xaratustrah/rdts/rsrc/rdts.kicad_sch

## KiCad design rsrc/rdts.kicad_sch (2023-10-17)

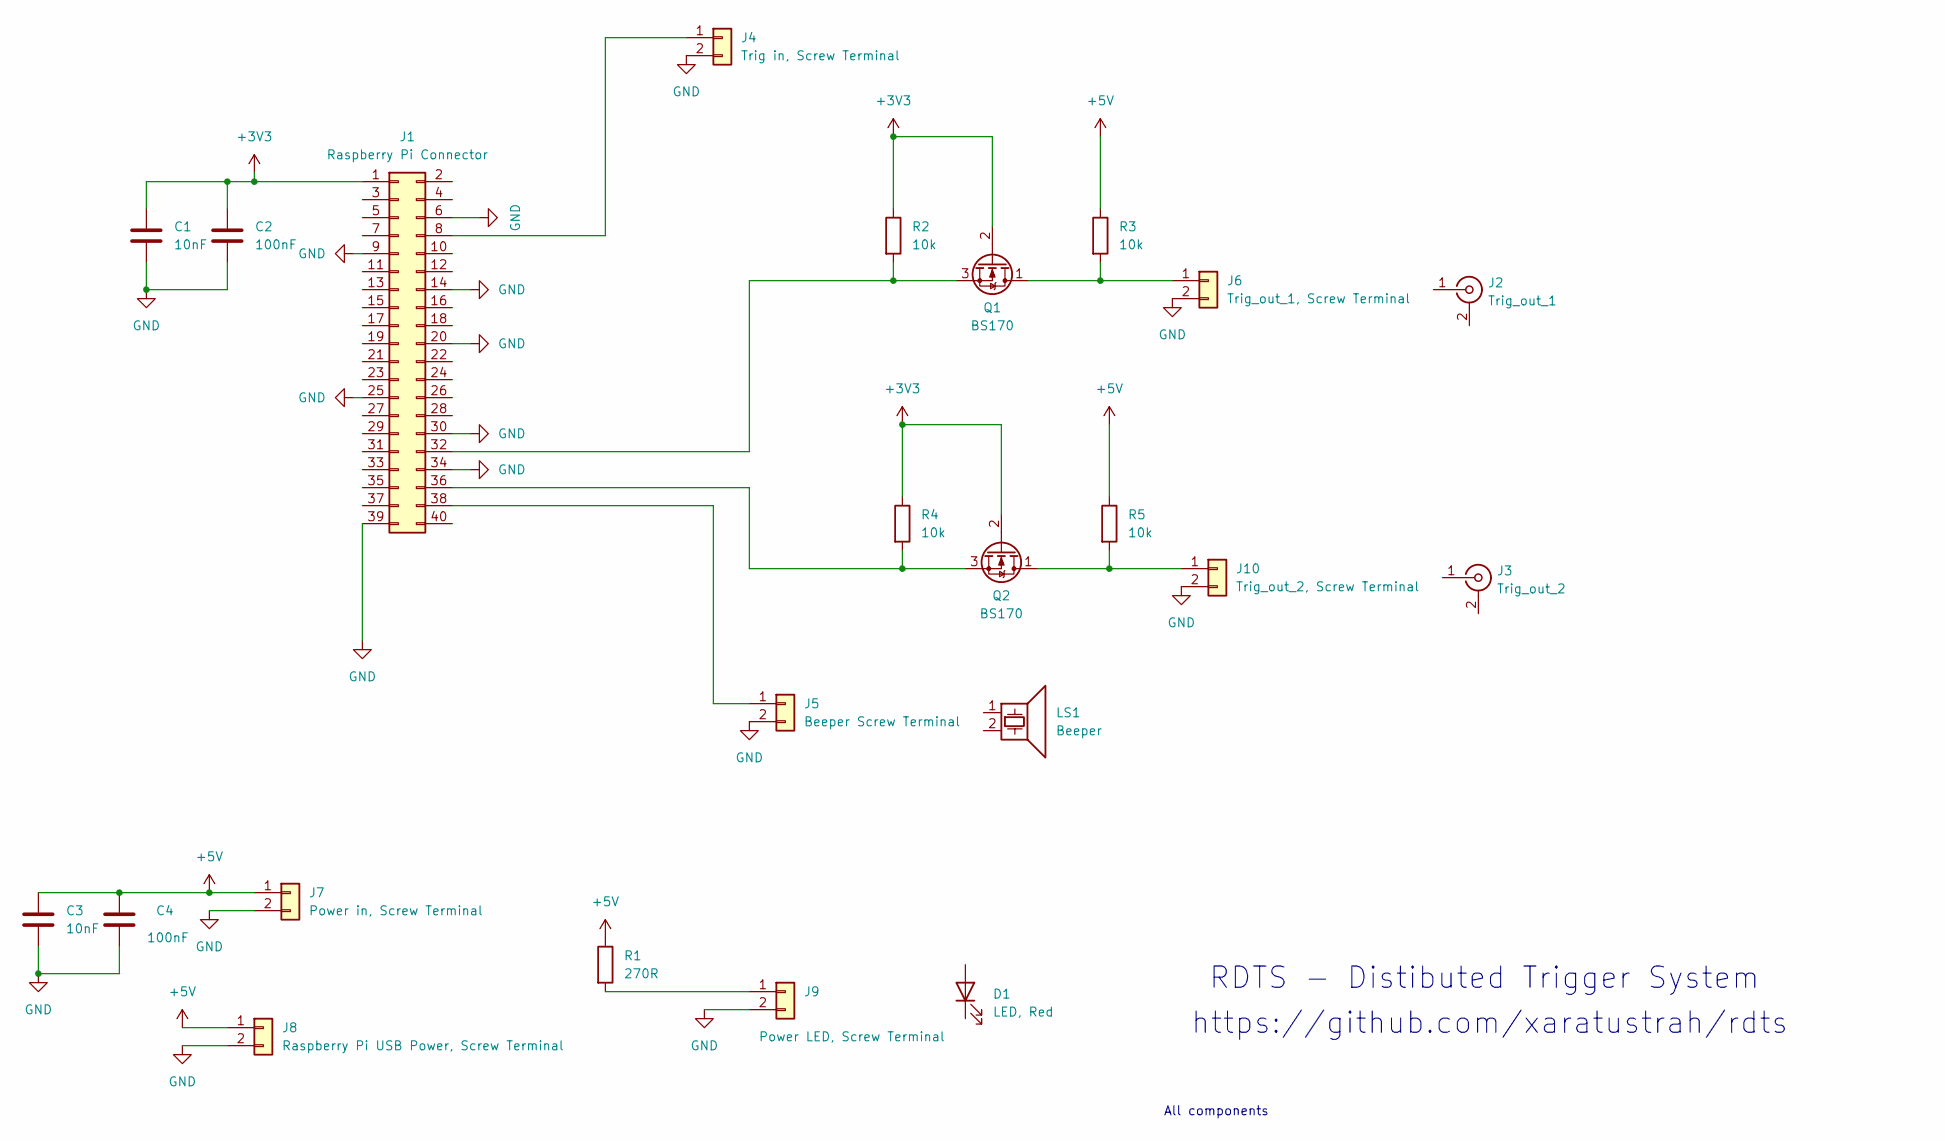
[picture p2: schematic rdts.kicad_sch]

Parts:
C1, C3: 10nF
C2, C4: 100nF
D1: LED, Red
J1: Raspberry Pi Connector
J2: Trig_out_1
J3: Trig_out_2
J4: Trig in, Screw Terminal
J5: Beeper Screw Terminal
J6: Trig_out_1, Screw Terminal
J7: Power in, Screw Terminal
J8: Raspberry Pi USB Power, Screw Terminal
J9: Power LED, Screw Terminal
J10: Trig_out_2, Screw Terminal
LS1: Beeper
Q1, Q2: BS170; TO-92_Inline
R1: 270R
R2, R3, R4, R5: 10k

Connections:
+3V3: C1.1, C2.1, J1.1, Q1.2 (G), Q2.2 (G), R2.1, R4.1
+5V: C3.1, C4.1, J7.1, J8.1, R1.1, R3.1, R5.1
GND: C1.2, C2.2, C3.2, C4.2, J1.6, J1.9, J1.14, J1.20, J1.25, J1.30, J1.34, J1.39, J4.2, J5.2, J6.2, J7.2, J8.2, J9.2, J10.2
unnamed: J1.8, J4.1
unnamed: J1.32, Q1.3 (S), R2.2
unnamed: J1.36, Q2.3 (S), R4.2
unnamed: J1.38, J5.1
unnamed: J6.1, Q1.1 (D), R3.2
unnamed: J9.1, R1.2
unnamed: J10.1, Q2.1 (D), R5.2

Notes on the sheet:
https://github.com/xaratustrah/rdts
All components
RDTS - Distibuted Trigger System
